tonoy12/Projects/esp32 AI field asistant/docs/images/3.jpeg

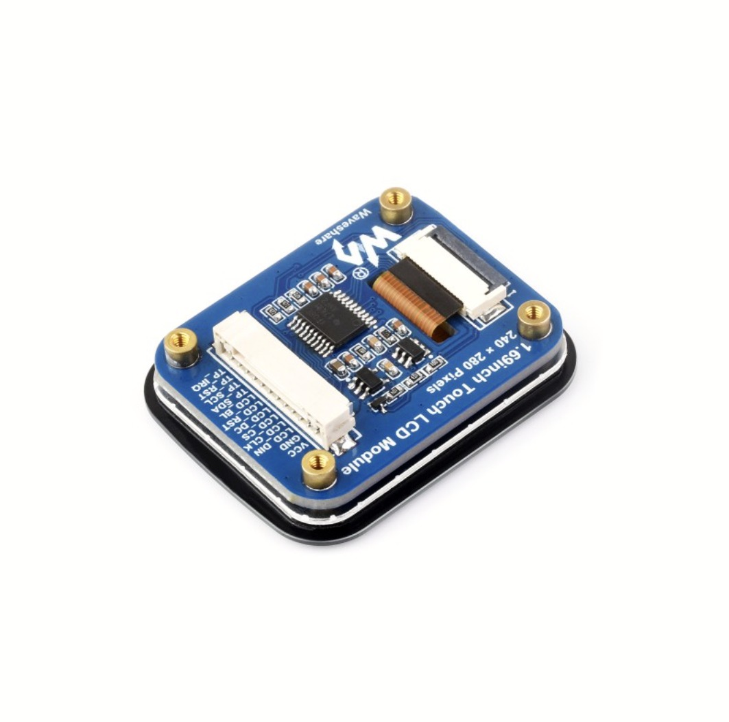
esp32 AI field asistant/docs/images/3.jpeg
