tonoy12/Projects/esp32 AI field asistant/docs/images/8.jpeg

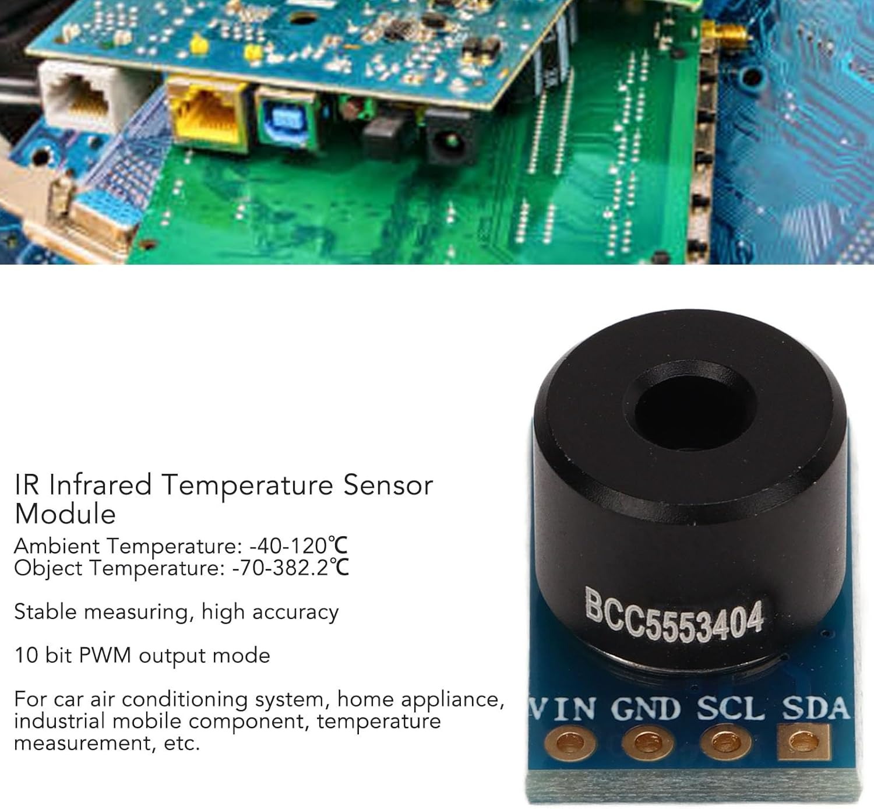
esp32 AI field asistant/docs/images/8.jpeg
