tonoy12/Projects/esp32 AI field asistant/docs/images/9.jpeg

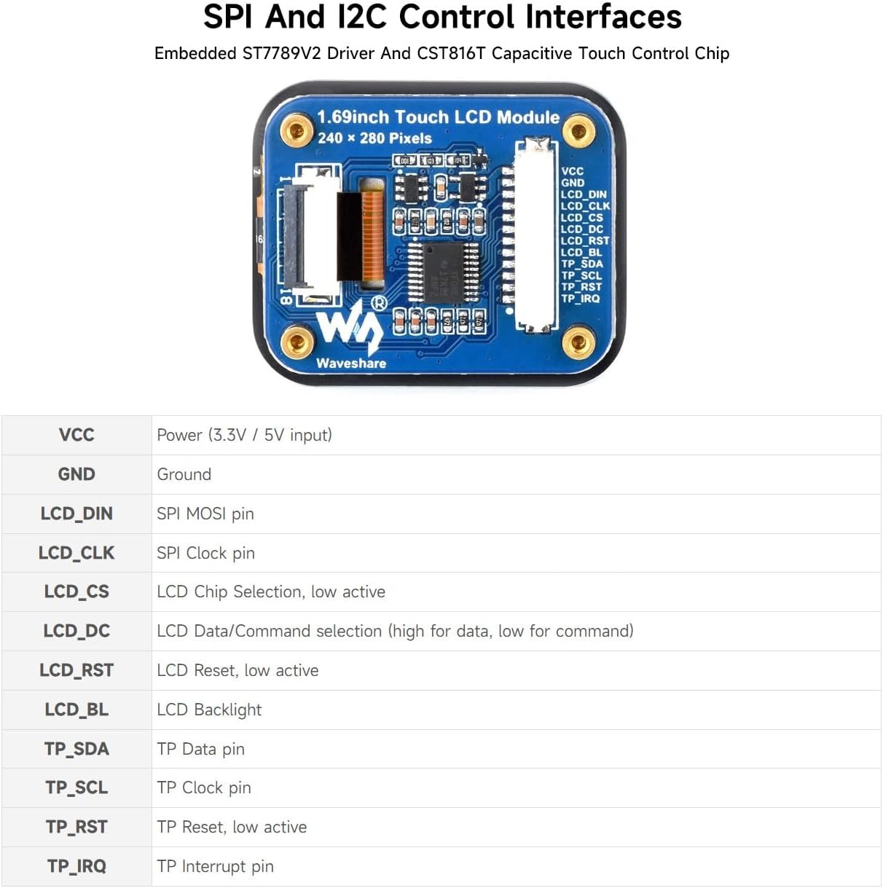
esp32 AI field asistant/docs/images/9.jpeg
