tonoy12/Projects/esp32 AI field asistant/docs/images/14.jpeg

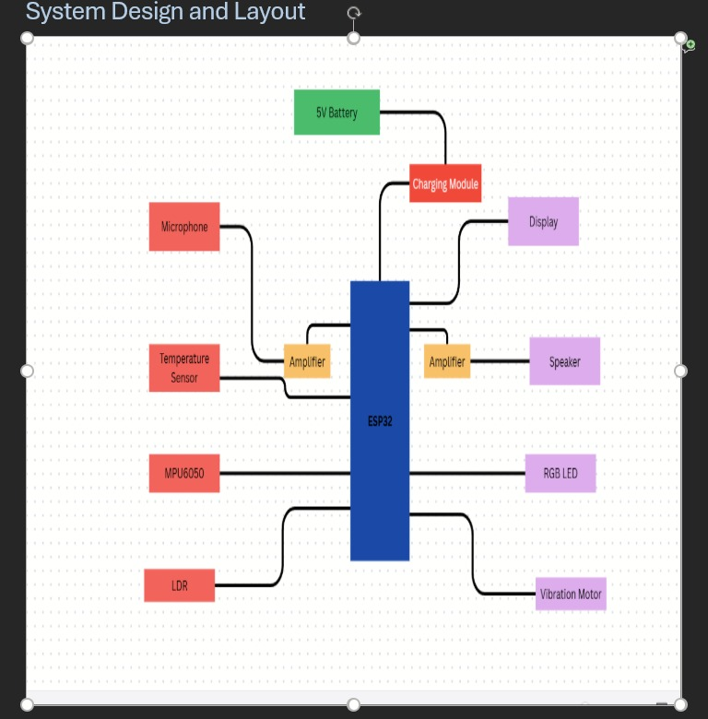
esp32 AI field asistant/docs/images/14.jpeg
