tonoy12/Projects/esp32 AI field asistant/docs/images/16.jpeg

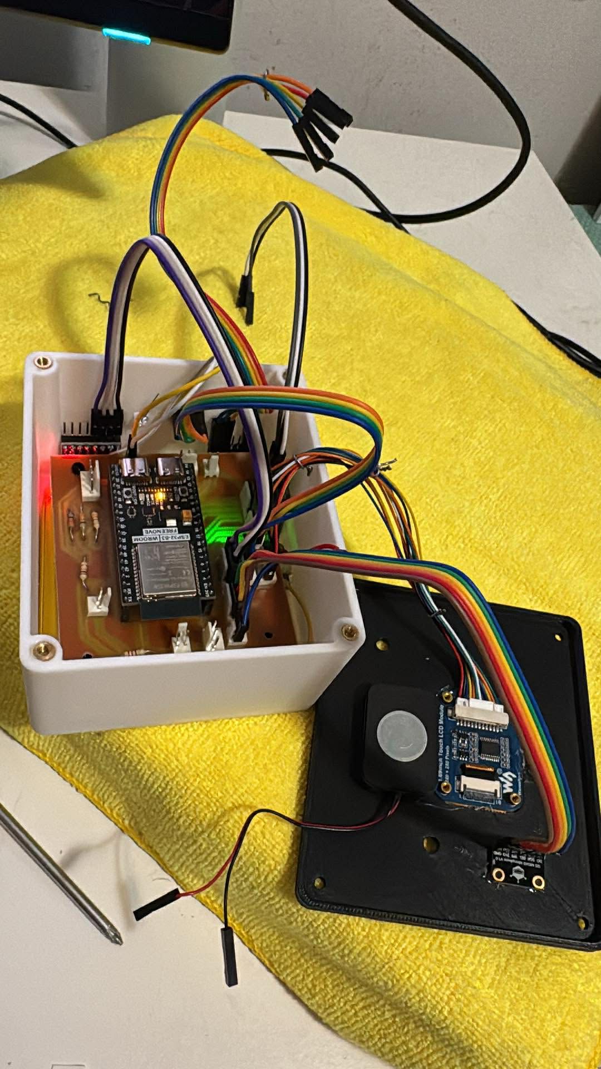
esp32 AI field asistant/docs/images/16.jpeg
