tonoy12/Projects/esp32 AI field asistant/docs/images/amplifire.jpeg

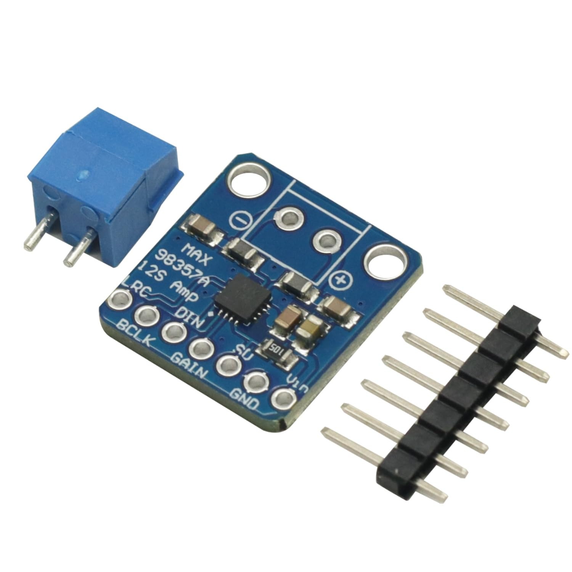
esp32 AI field asistant/docs/images/amplifire.jpeg
