tonoy12/Projects/esp32 AI field asistant/docs/images/booster converter 5v.jpeg

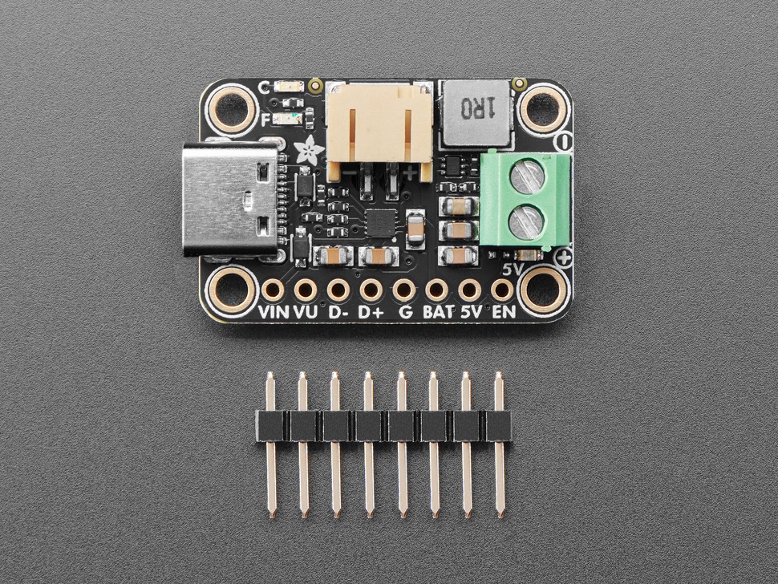
esp32 AI field asistant/docs/images/booster converter 5v.jpeg
