tonoy12/Projects/esp32 AI field asistant/docs/images/drf robo mems microphone.jpeg

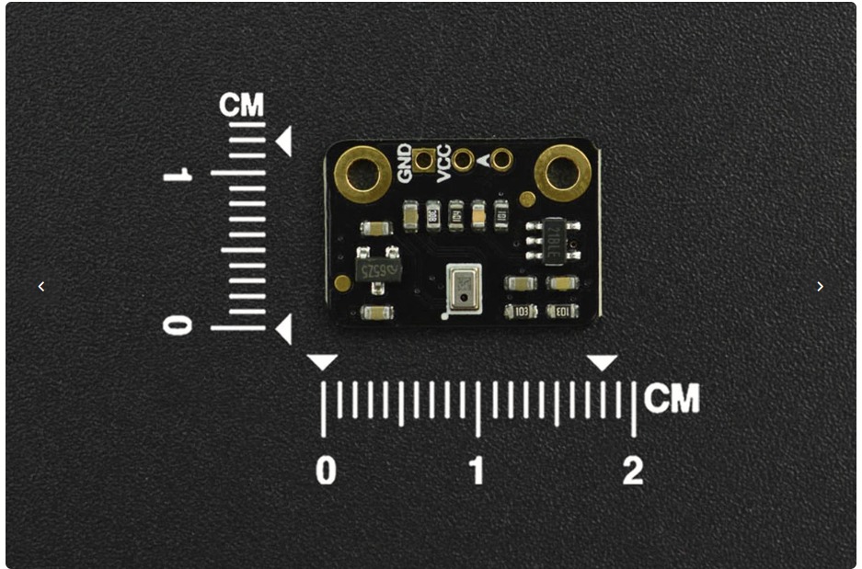
esp32 AI field asistant/docs/images/drf robo mems microphone.jpeg
