tonoy12/Projects/esp32 AI field asistant/docs/images/IR temp sensor.jpeg

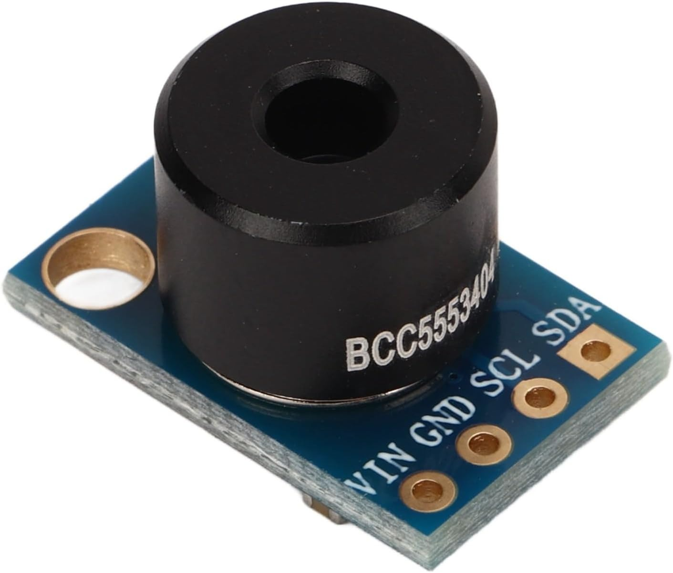
esp32 AI field asistant/docs/images/IR temp sensor.jpeg
