tonoy12/Projects/esp32 AI field asistant/docs/images/LDR.jpeg

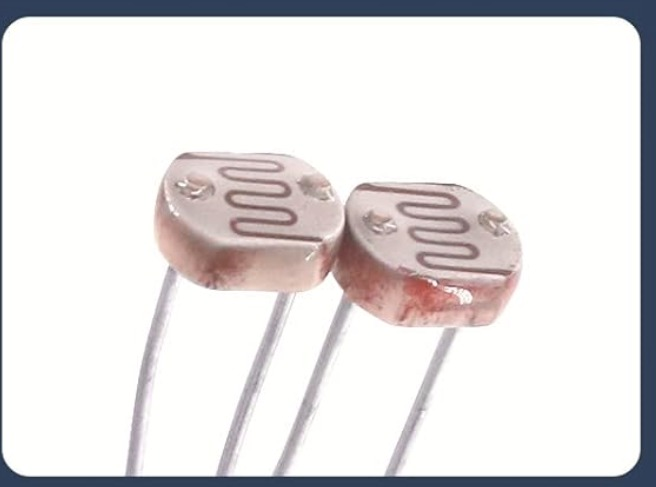
esp32 AI field asistant/docs/images/LDR.jpeg
