tonoy12/Projects/esp32 AI field asistant/docs/images/mpu6050.jpeg

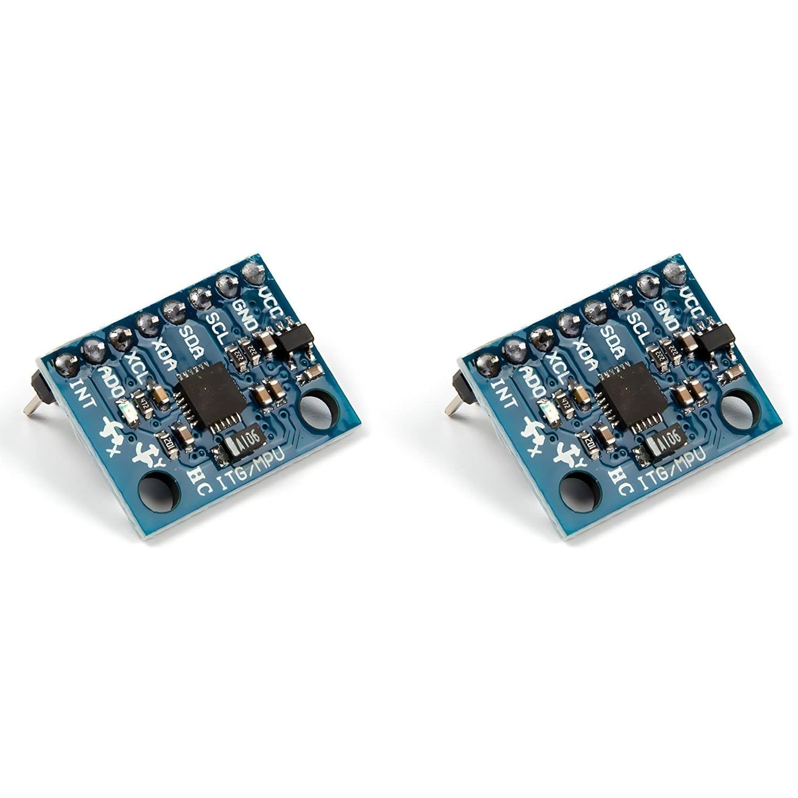
esp32 AI field asistant/docs/images/mpu6050.jpeg
