tonoy12/Projects/esp32 AI field asistant/docs/images/power sourse.jpeg

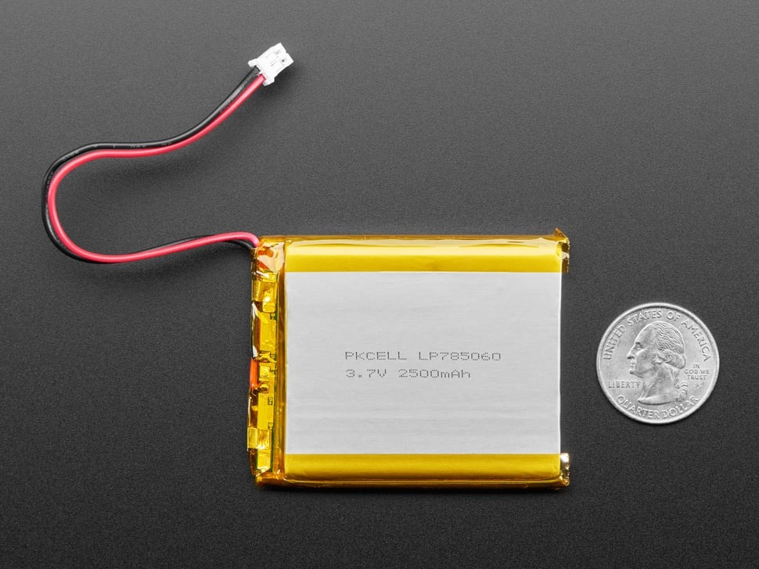
esp32 AI field asistant/docs/images/power sourse.jpeg
