tonoy12/Projects/esp32 AI field asistant/docs/images/rgb.jpeg

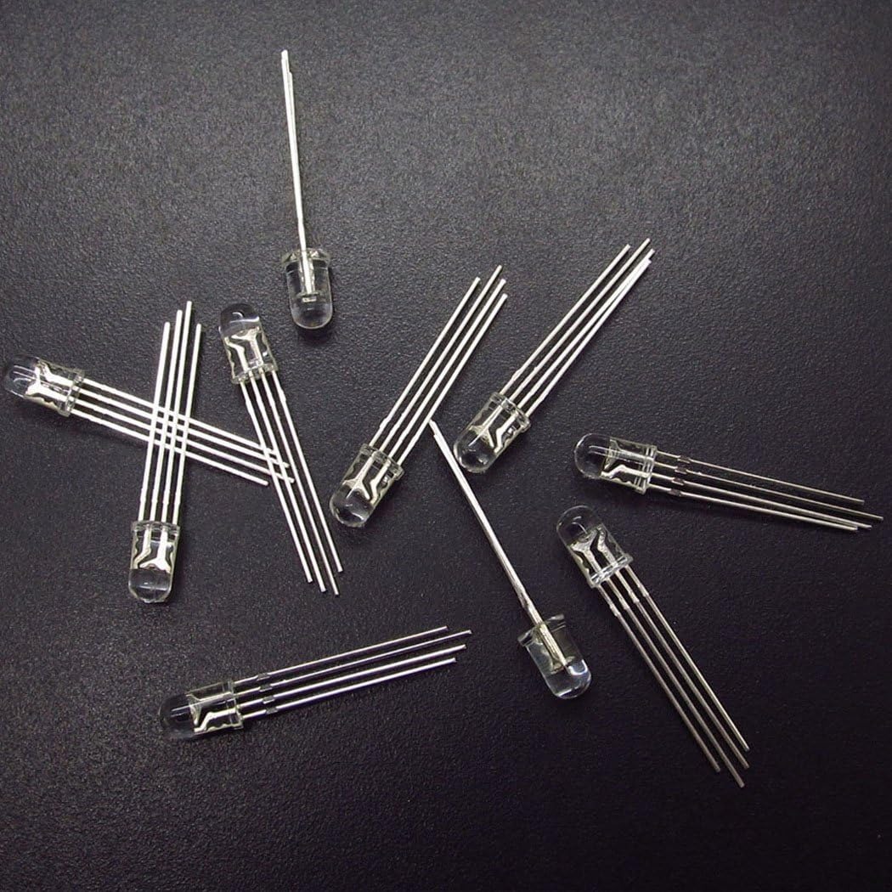
esp32 AI field asistant/docs/images/rgb.jpeg
