tonoy12/Projects/esp32 AI field asistant/docs/images/speaker.jpeg

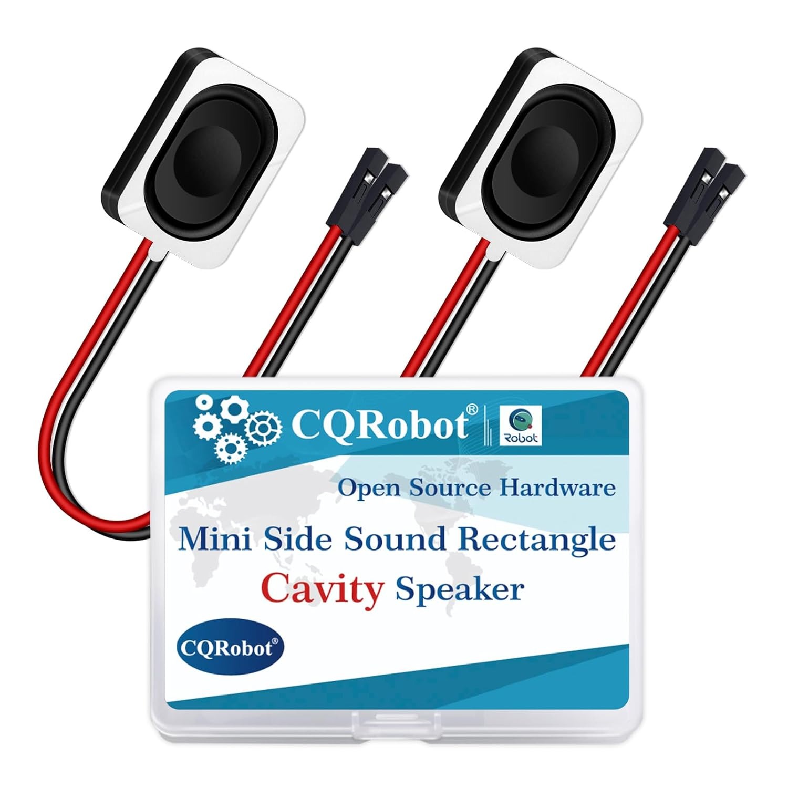
esp32 AI field asistant/docs/images/speaker.jpeg
