tonoy12/Projects/esp32 AI field asistant/Enclosure/1.jpeg

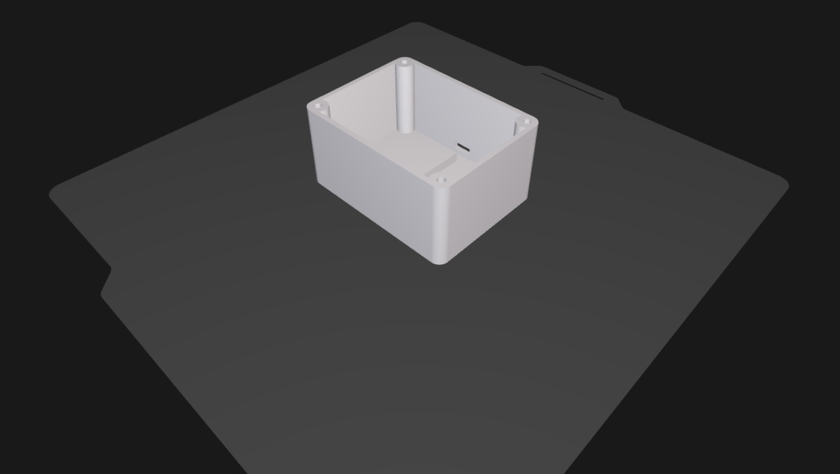
esp32 AI field asistant/Enclosure/1.jpeg
