tonoy12/Projects/esp32 AI field asistant/Enclosure/2.jpeg

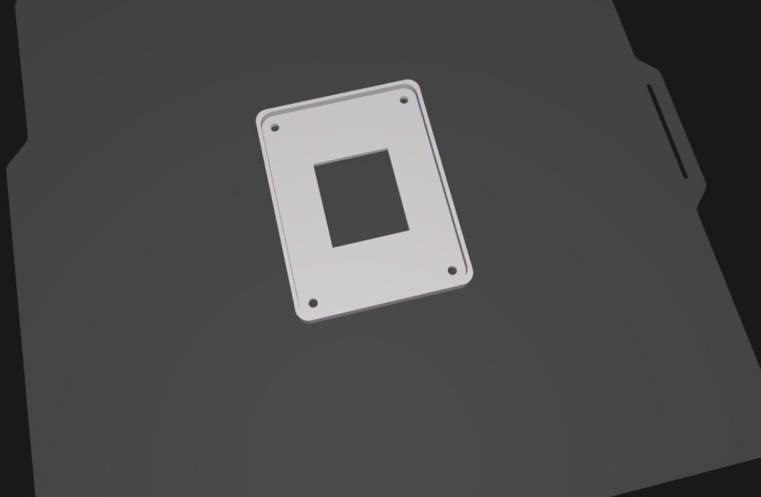
esp32 AI field asistant/Enclosure/2.jpeg
