tonoy12/Projects/esp32 AI field asistant/Hardware/Custom pcb footprint esp32 s3 freenove/1.png

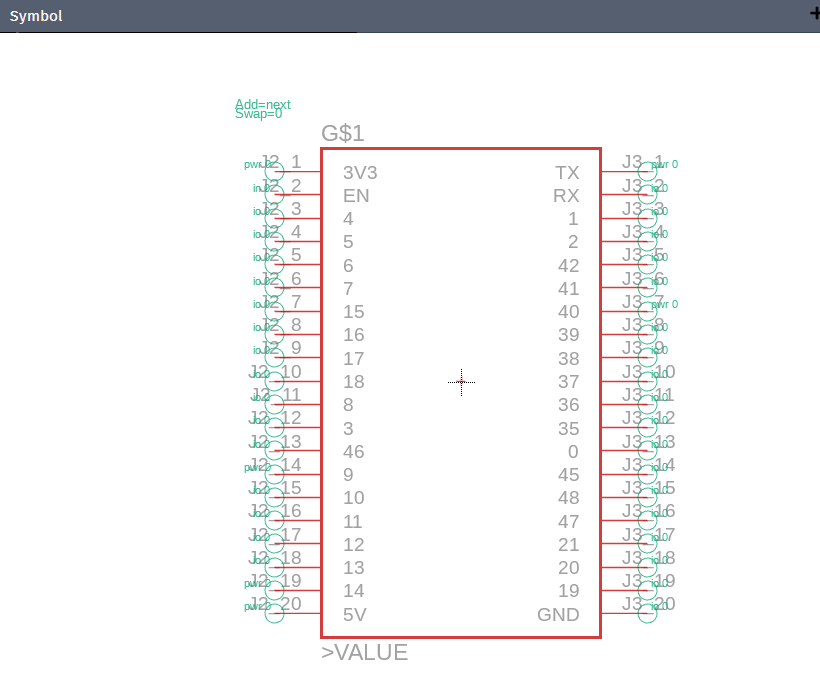
esp32 AI field asistant/Hardware/Custom pcb footprint esp32 s3 freenove/1.png
